NellowTCS/HonzoReader/Docs/assets/images/PlatformIO_new_project.png

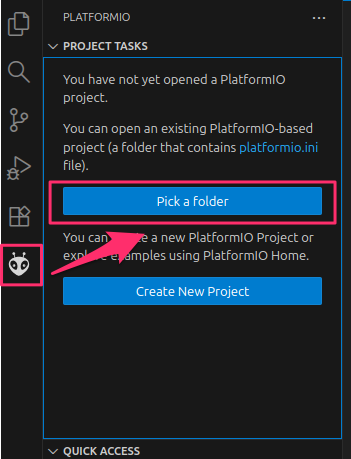
Docs/assets/images/PlatformIO_new_project.png
