NellowTCS/HonzoReader/Resources/Assets/App Loader/Image200.bmp

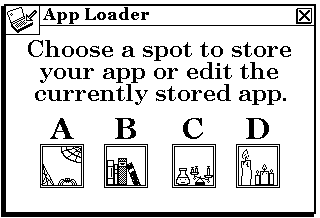
Resources/Assets/App Loader/Image200.bmp
