NellowTCS/HonzoReader/Resources/Assets/Calendar/calendar01.bmp

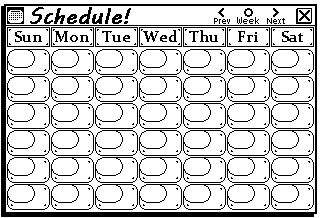
Resources/Assets/Calendar/calendar01.bmp
