NellowTCS/HonzoReader/Resources/Assets/Calendar/calendar02.bmp

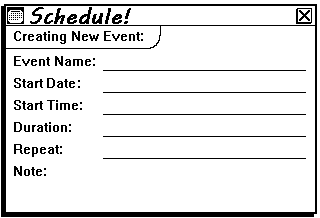
Resources/Assets/Calendar/calendar02.bmp
