NellowTCS/HonzoReader/Resources/Assets/Calendar/calendar03.bmp

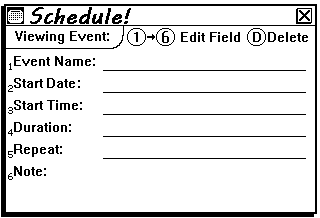
Resources/Assets/Calendar/calendar03.bmp
