NellowTCS/HonzoReader/Resources/Assets/Calendar/calendar04.bmp

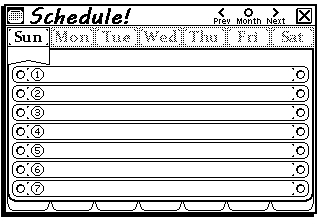
Resources/Assets/Calendar/calendar04.bmp
