NellowTCS/HonzoReader/Resources/Assets/File Wizard/fileWiz0.bmp

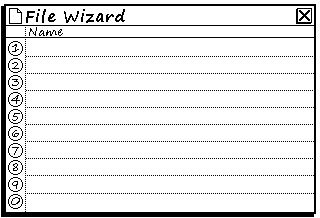
Resources/Assets/File Wizard/fileWiz0.bmp
