NellowTCS/HonzoReader/Resources/Assets/File Wizard/fileWiz1.bmp

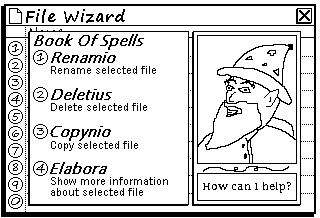
Resources/Assets/File Wizard/fileWiz1.bmp
