NellowTCS/HonzoReader/Resources/Assets/File Wizard/fileWiz3.bmp

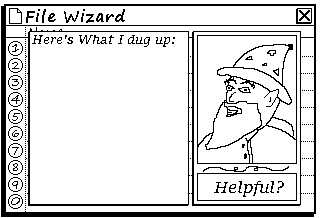
Resources/Assets/File Wizard/fileWiz3.bmp
