NellowTCS/HonzoReader/Resources/Assets/File Wizard/fileWizLite0.bmp

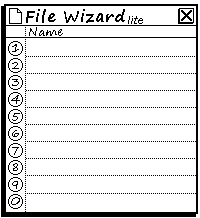
Resources/Assets/File Wizard/fileWizLite0.bmp
