NellowTCS/HonzoReader/Resources/Assets/File Wizard/fileWizLite1.bmp

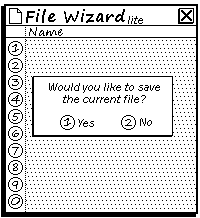
Resources/Assets/File Wizard/fileWizLite1.bmp
