NellowTCS/HonzoReader/Resources/Assets/File Wizard/fileWizLite2.bmp

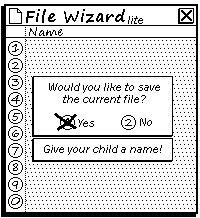
Resources/Assets/File Wizard/fileWizLite2.bmp
