NellowTCS/HonzoReader/Resources/Assets/Font Czar/font0.bmp

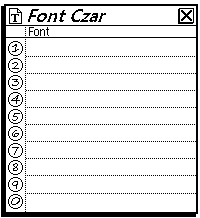
Resources/Assets/Font Czar/font0.bmp
