NellowTCS/HonzoReader/Resources/Assets/Now and Later/nowAndLater0.bmp

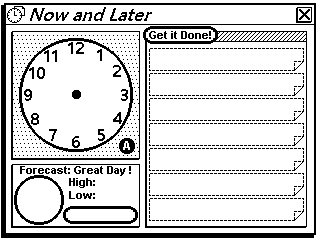
Resources/Assets/Now and Later/nowAndLater0.bmp
