NellowTCS/HonzoReader/Resources/Assets/ScreenSaver/New folder/betterworld_JosieBB.bmp

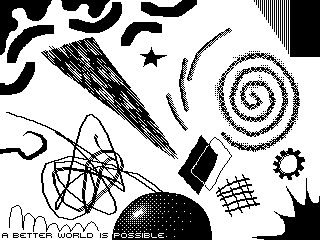
Resources/Assets/ScreenSaver/New folder/betterworld_JosieBB.bmp
