NellowTCS/HonzoReader/Resources/Assets/ScreenSaver/New folder/castle_Nora.bmp

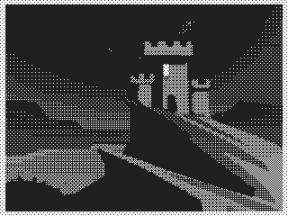
Resources/Assets/ScreenSaver/New folder/castle_Nora.bmp
