NellowTCS/HonzoReader/Resources/Assets/ScreenSaver/New folder/classic (1).bmp

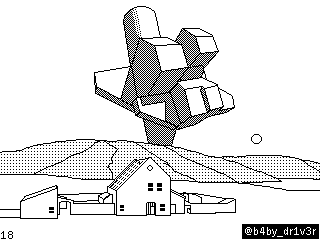
Resources/Assets/ScreenSaver/New folder/classic (1).bmp
