NellowTCS/HonzoReader/Resources/Assets/ScreenSaver/New folder/classic (2).bmp

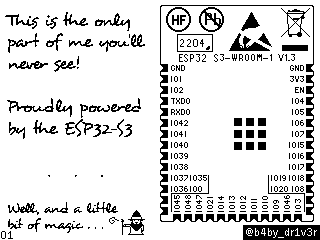
Resources/Assets/ScreenSaver/New folder/classic (2).bmp
