NellowTCS/HonzoReader/Resources/Assets/ScreenSaver/New folder/classic (3).bmp

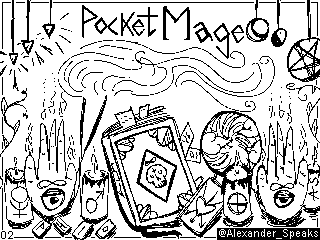
Resources/Assets/ScreenSaver/New folder/classic (3).bmp
