NellowTCS/HonzoReader/Resources/Assets/ScreenSaver/New folder/classic (4).bmp

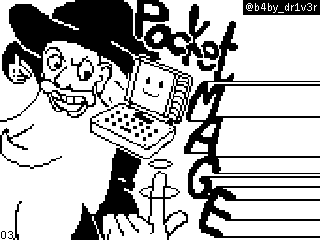
Resources/Assets/ScreenSaver/New folder/classic (4).bmp
