NellowTCS/HonzoReader/Resources/Assets/ScreenSaver/New folder/classic (5).bmp

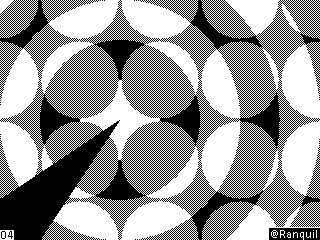
Resources/Assets/ScreenSaver/New folder/classic (5).bmp
