NellowTCS/HonzoReader/Resources/Assets/ScreenSaver/New folder/classic (6).bmp

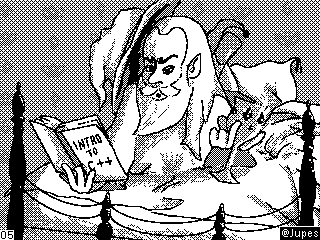
Resources/Assets/ScreenSaver/New folder/classic (6).bmp
