NellowTCS/HonzoReader/Resources/Assets/ScreenSaver/New folder/classic (7).bmp

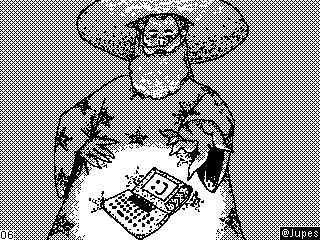
Resources/Assets/ScreenSaver/New folder/classic (7).bmp
