NellowTCS/HonzoReader/Resources/Assets/ScreenSaver/New folder/classic (9).bmp

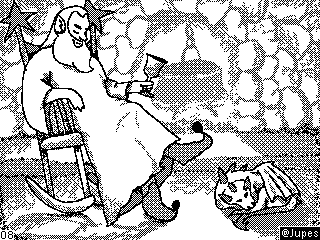
Resources/Assets/ScreenSaver/New folder/classic (9).bmp
