NellowTCS/HonzoReader/Resources/Assets/ScreenSaver/New folder/classic (10).bmp

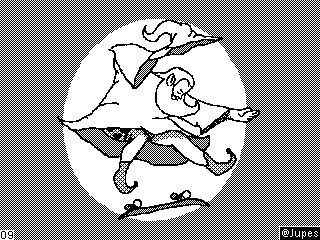
Resources/Assets/ScreenSaver/New folder/classic (10).bmp
