NellowTCS/HonzoReader/Resources/Assets/ScreenSaver/New folder/classic (11).bmp

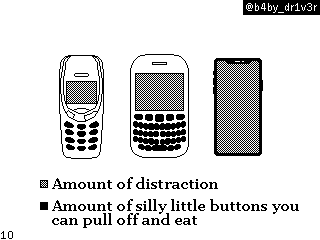
Resources/Assets/ScreenSaver/New folder/classic (11).bmp
