NellowTCS/HonzoReader/Resources/Assets/ScreenSaver/New folder/classic (12).bmp

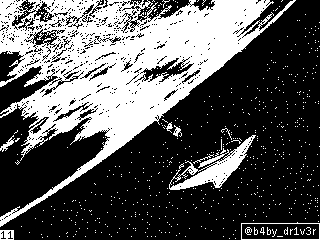
Resources/Assets/ScreenSaver/New folder/classic (12).bmp
