NellowTCS/HonzoReader/Resources/Assets/ScreenSaver/New folder/classic (13).bmp

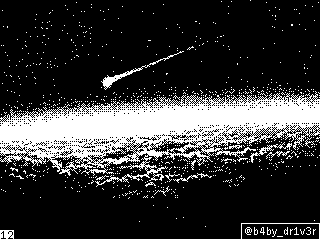
Resources/Assets/ScreenSaver/New folder/classic (13).bmp
