NellowTCS/HonzoReader/Resources/Assets/ScreenSaver/New folder/classic (14).bmp

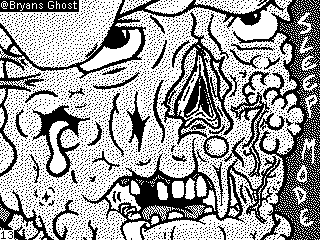
Resources/Assets/ScreenSaver/New folder/classic (14).bmp
