NellowTCS/HonzoReader/Resources/Assets/ScreenSaver/New folder/classic (15).bmp

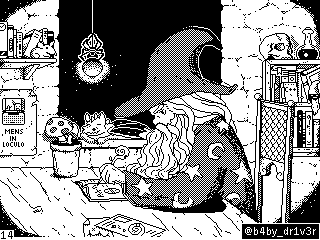
Resources/Assets/ScreenSaver/New folder/classic (15).bmp
