NellowTCS/HonzoReader/Resources/Assets/ScreenSaver/New folder/classic (16).bmp

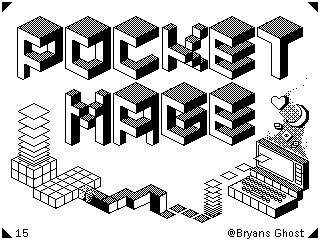
Resources/Assets/ScreenSaver/New folder/classic (16).bmp
