NellowTCS/HonzoReader/Resources/Assets/ScreenSaver/New folder/classic (17).bmp

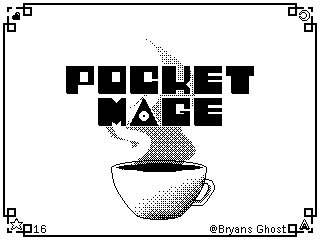
Resources/Assets/ScreenSaver/New folder/classic (17).bmp
