NellowTCS/HonzoReader/Resources/Assets/ScreenSaver/New folder/dragon_TheOddFireFox.bmp

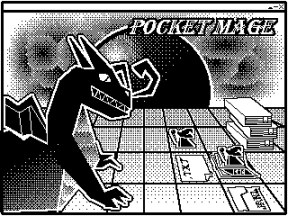
Resources/Assets/ScreenSaver/New folder/dragon_TheOddFireFox.bmp
