NellowTCS/HonzoReader/Resources/Assets/Sleep/sleep0.bmp

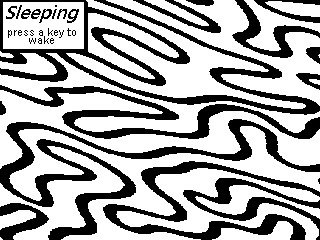
Resources/Assets/Sleep/sleep0.bmp
