NellowTCS/HonzoReader/Resources/Assets/Tasks/1.bmp

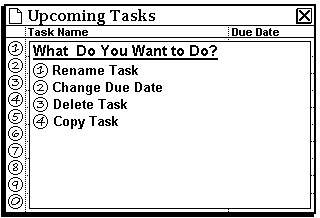
Resources/Assets/Tasks/1.bmp
