NellowTCS/HonzoReader/Resources/Assets/usb/Image20.bmp

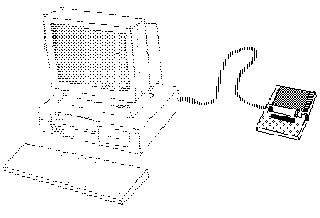
Resources/Assets/usb/Image20.bmp
