NellowTCS/HonzoReader/Docs/assets/images/PlatformIO_installing.png

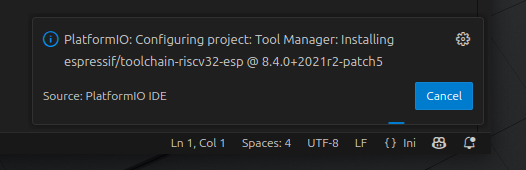
Docs/assets/images/PlatformIO_installing.png
