NellowTCS/HonzoReader/Resources/Assets/Journal/journal0.bmp

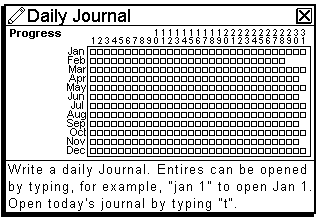
Resources/Assets/Journal/journal0.bmp
