NellowTCS/HonzoReader/Code/PocketMage_V3/src/OS_APPS/JOURNAL.cpp

// AUDIT 1

#include <globals.h>
#if !OTA_APP // POCKETMAGE_OS
enum JournalState {J_MENU, J_TXT};
JournalState CurrentJournalState = J_MENU;

String currentJournal = "";
String bufferEditingFile = PM_SDAUTO().getEditingFile();

void JOURNAL_INIT() {
  CurrentAppState = JOURNAL;
  CurrentJournalState = J_MENU;
  #if POCKETMAGE_HW_VERSION != 2
    EINK().forceSlowFullUpdate(true);
  #endif
  newState = true;
  KB().setKeyboardState(NORMAL);
  bufferEditingFile = PM_SDAUTO().getEditingFile();
}

// File Operations
void loadJournal() {
  PM_SDAUTO().setEditingFile(currentJournal);
  PM_SDAUTO().loadFile();
}

void saveJournal() {
  PM_SDAUTO().setEditingFile(currentJournal);
  PM_SDAUTO().saveFile();
}

String getCurrentJournal() {return currentJournal;}

// Functions
bool isLeapYear(int year) {
  return ((year % 4 == 0) && (year % 100 != 0)) || (year % 400 == 0);
}

void drawJMENU() {
  SDActive = true;
  pocketmage::setCpuSpeed(240);
  delay(50);

  // Display background
  display.setTextColor(GxEPD_BLACK);
  EINK().drawStatusBar("Choose (D)ate or (T)oday");
  display.drawBitmap(0, 0, _journal, 320, 218, GxEPD_BLACK);

  // Update current progress graph
  DateTime now = CLOCK().nowDT();
  String year = String(now.year());

  // 1-indexed matrix to store which days have journal entries
  bool hasJournal[13][32] = {false}; 

  // Read the directory exactly ONCE to prevent SD Card / VFS thrashing
  File dir = global_fs->open("/journal");
  if (dir && dir.isDirectory()) {
    File entry;
    while ((entry = dir.openNextFile())) {
      if (!entry.isDirectory()) {
        String name = entry.name();
        
        // Handle potential leading slash from filesystem driver
        if (name.startsWith("/")) name = name.substring(1);
        
        // Ensure format is exactly YYYYMMDD.txt (12 chars)
        if (name.length() == 12 && name.endsWith(".txt")) {
          if (name.substring(0, 4) == year) {
            int m = name.substring(4, 6).toInt();
            int d = name.substring(6, 8).toInt();
            // Bound checking before writing to array
            if (m >= 1 && m <= 12 && d >= 1 && d <= 31) {
              hasJournal[m][d] = true;
            }
          }
        }
      }
      entry.close();
    }
    dir.close();
  }

  // Pre-calculated Y offsets for each month row
  int yOffsets[12] = {50, 59, 68, 77, 86, 95, 104, 113, 122, 131, 140, 149};
  int daysInMonths[12] = {
    31, isLeapYear(now.year()) ? 29 : 28, 31, 30, 31, 30, 
    31, 31, 30, 31, 30, 31
  };

  // Plot the graph from the matrix
  for (int m = 1; m <= 12; m++) {
    for (int d = 1; d <= daysInMonths[m - 1]; d++) {
      if (hasJournal[m][d]) {
        display.fillRect(91 + (7 * (d - 1)), yOffsets[m - 1], 4, 4, GxEPD_BLACK);
      }
    }
  }

  if (SAVE_POWER) pocketmage::setCpuSpeed(POWER_SAVE_FREQ);
  SDActive = false;
}

// Loops
void processKB_JOURNAL() {
  if (CurrentJournalState == J_MENU && !newState) {
    int currentMillis = millis();
    String uiDate = "";
    
    // 1. Drain the hardware buffer continuously at loop speed
    char inchar = KB().updateKeypress();

    // 2. Only process the actual input if the cooldown has expired
    if (currentMillis - KBBounceMillis >= KB_COOLDOWN) {  
      if (inchar != 0) {
        KBBounceMillis = currentMillis;

        if (inchar == 12 || inchar == 28 || inchar == 19 || inchar == 24) { 
          HOME_INIT();
          return;
        }
        else if (inchar == 't' || inchar == 'T' || inchar == 9 || inchar == 14) {
          DateTime now = CLOCK().nowDT();
          char dateBuf[11];
          snprintf(dateBuf, sizeof(dateBuf), "%02d/%02d/%04d", now.day(), now.month(), now.year());
          uiDate = String(dateBuf);
        }
        else if (inchar == 'd' || inchar == 'D') {
          uiDate = datePrompt("");
          if (CurrentAppState != JOURNAL) return;
        }

        if (uiDate.length() == 10) {
          SDActive = true;
          pocketmage::setCpuSpeed(240);
          delay(50);

          // Convert DD/MM/YYYY from datePrompt into YYYYMMDD for the file system
          String d = uiDate.substring(0, 2);
          String m = uiDate.substring(3, 5);
          String y = uiDate.substring(6, 10);
          String fileName = "/journal/" + y + m + d + ".txt";

          // If file doesn't exist, create it
          if (!global_fs->exists(fileName)) {
            File f = global_fs->open(fileName, FILE_WRITE);
            if (f) f.close();
          }

          currentJournal = fileName;

          if (SAVE_POWER) pocketmage::setCpuSpeed(POWER_SAVE_FREQ);
          SDActive = false;
          
          // Pass execution to the text editor
          TXT_INIT_JournalMode();
          return;
        }
      }
    }

    // 3. Update OLED at true OLED_MAX_FPS, completely independent of keyboard bounce
    currentMillis = millis();
    if (currentMillis - OLEDFPSMillis >= (1000/OLED_MAX_FPS)) {
      OLEDFPSMillis = currentMillis;
      OLED().oledLine("", 0, false);
    }
  }
}

void einkHandler_JOURNAL() {
  switch (CurrentJournalState) {
    case J_MENU:
      if (newState) {
        newState = false;

        EINK().resetDisplay(); // Clear the uninitialized buffer correctly
        drawJMENU();

        EINK().multiPassRefresh(2);
      }
      break;
    default:
      CurrentJournalState = J_MENU;
      break;
  } 
}
#endif
