NellowTCS/HonzoReader/Resources/Subsystem Tests/BuzzerTest_SuperMario/BuzzerTest_SuperMario.ino

#include <Buzzer.h>

Buzzer buzzer(17);

void setup() {}

void loop() {
  buzzer.begin(100);

  buzzer.sound(NOTE_E7, 80);
  buzzer.sound(NOTE_E7, 80);
  buzzer.sound(0, 80);
  buzzer.sound(NOTE_E7, 80);
  buzzer.sound(0, 80);
  buzzer.sound(NOTE_C7, 80);
  buzzer.sound(NOTE_E7, 80);
  buzzer.sound(0, 80);
  buzzer.sound(NOTE_G7, 80);
  buzzer.sound(0, 240);
  buzzer.sound(NOTE_G6, 80);
  buzzer.sound(0, 240);
  buzzer.sound(NOTE_C7, 80);
  buzzer.sound(0, 160);
  buzzer.sound(NOTE_G6, 80);
  buzzer.sound(0, 160);
  buzzer.sound(NOTE_E6, 80);
  buzzer.sound(0, 160);
  buzzer.sound(NOTE_A6, 80);
  buzzer.sound(0, 80);
  buzzer.sound(NOTE_B6, 80);
  buzzer.sound(0, 80);
  buzzer.sound(NOTE_AS6, 80);
  buzzer.sound(NOTE_A6, 80);
  buzzer.sound(0, 80);
  buzzer.sound(NOTE_G6, 100);
  buzzer.sound(NOTE_E7, 100);
  buzzer.sound(NOTE_G7, 100);
  buzzer.sound(NOTE_A7, 80);
  buzzer.sound(0, 80);
  buzzer.sound(NOTE_F7, 80);
  buzzer.sound(NOTE_G7, 80);
  buzzer.sound(0, 80);
  buzzer.sound(NOTE_E7, 80);
  buzzer.sound(0, 80);
  buzzer.sound(NOTE_C7, 80);
  buzzer.sound(NOTE_D7, 80);
  buzzer.sound(NOTE_B6, 80);
  buzzer.sound(0, 160);
  buzzer.sound(NOTE_C7, 80);
  buzzer.sound(0, 160);
  buzzer.sound(NOTE_G6, 80);
  buzzer.sound(0, 160);
  buzzer.sound(NOTE_E6, 80);
  buzzer.sound(0, 160);
  buzzer.sound(NOTE_A6, 80);
  buzzer.sound(0, 80);
  buzzer.sound(NOTE_B6, 80);
  buzzer.sound(0, 80);
  buzzer.sound(NOTE_AS6, 80);
  buzzer.sound(NOTE_A6, 80);
  buzzer.sound(0, 80);
  buzzer.sound(NOTE_G6, 100);
  buzzer.sound(NOTE_E7, 100);
  buzzer.sound(NOTE_G7, 100);
  buzzer.sound(NOTE_A7, 80);
  buzzer.sound(0, 80);
  buzzer.sound(NOTE_F7, 80);
  buzzer.sound(NOTE_G7, 80);
  buzzer.sound(0, 80);
  buzzer.sound(NOTE_E7, 80);
  buzzer.sound(0, 80);
  buzzer.sound(NOTE_C7, 80);
  buzzer.sound(NOTE_D7, 80);
  buzzer.sound(NOTE_B6, 80);
  buzzer.sound(0, 160);

  buzzer.end(2000);
}
