NellowTCS/HonzoReader/Resources/Subsystem Tests/MPR121test/MPR121test.ino

#include <Wire.h>
#include "Adafruit_MPR121.h"

#ifndef _BV
#define _BV(bit) (1 << (bit)) 
#endif

#define I2C_SCL       35
#define I2C_SDA       36
#define MPR121_ADDR   0x5A

// You can have up to 4 on one i2c bus but one is enough for testing!
Adafruit_MPR121 cap = Adafruit_MPR121();

// Keeps track of the last pins touched
// so we know when buttons are 'released'
uint16_t lasttouched = 0;
uint16_t currtouched = 0;

void setup() {
  Serial.begin(9600);
  Wire.begin(I2C_SDA, I2C_SCL);

  while (!Serial) { // needed to keep leonardo/micro from starting too fast!
    delay(10);
  }
  
  Serial.println("Adafruit MPR121 Capacitive Touch sensor test"); 
  
  // Default address is 0x5A, if tied to 3.3V its 0x5B
  // If tied to SDA its 0x5C and if SCL then 0x5D
  if (!cap.begin(MPR121_ADDR)) {
    Serial.println("MPR121 not found, check wiring?");
    while (1);
  }
  Serial.println("MPR121 found!");

  cap.setAutoconfig(true);
  delay(1000);
  //Serial.println("MPR121 being initialized");
  //cap.setThreshholds(1,1);
}

void loop() {
  // Get the currently touched pads
  currtouched = cap.touched();
  
  for (uint8_t i=0; i<12; i++) {
    // it if *is* touched and *wasnt* touched before, alert!
    if ((currtouched & _BV(i)) && !(lasttouched & _BV(i)) ) {
      Serial.print(i); Serial.println(" touched");
    }
    // if it *was* touched and now *isnt*, alert!
    if (!(currtouched & _BV(i)) && (lasttouched & _BV(i)) ) {
      Serial.print(i); Serial.println(" released");
    }
  }

  // reset our state
  lasttouched = currtouched;

  // comment out this line for detailed data from the sensor!
  return;
  
  // debugging info, what
  Serial.print("\t\t\t\t\t\t\t\t\t\t\t\t\t 0x"); Serial.println(cap.touched(), HEX);
  Serial.print("Filt: ");
  for (uint8_t i=0; i<12; i++) {
    Serial.print(cap.filteredData(i)); Serial.print("\t");
  }
  Serial.println();
  Serial.print("Base: ");
  for (uint8_t i=0; i<12; i++) {
    Serial.print(cap.baselineData(i)); Serial.print("\t");
  }
  Serial.println();
  
  // put a delay so it isn't overwhelming
  delay(100);
}
