NellowTCS/HonzoReader/Resources/Subsystem Tests/GDEQ031T10-Arduino/Ap_29demo.h

#include <pgmspace.h>
//32*32(y=32-1,x=32-1)
const unsigned char gImage_num0[128]PROGMEM = { /* 0X00,0X01,0X20,0X00,0X20,0X00, */
0XFF,0XFF,0XFF,0XFF,0XFF,0XFF,0XFF,0XFF,0XFF,0XFF,0XFF,0XFF,0XFF,0XFF,0XFF,0XFF,
0XFF,0XFF,0XFF,0XFF,0XFF,0XFF,0XFF,0XFF,0XFF,0XFF,0XFF,0XFF,0XFF,0XFF,0XFF,0XFF,
0XFF,0XFC,0X0F,0XFF,0XFF,0XF8,0XC7,0XFF,0XFF,0XF1,0XE3,0XFF,0XFF,0XE3,0XF1,0XFF,
0XFF,0XE3,0XF1,0XFF,0XFF,0XE3,0XF9,0XFF,0XFF,0XC7,0XF8,0XFF,0XFF,0XC7,0XF8,0XFF,
0XFF,0XC7,0XF8,0XFF,0XFF,0XC7,0XF8,0XFF,0XFF,0XC7,0XF8,0XFF,0XFF,0XC7,0XF8,0XFF,
0XFF,0XC7,0XF8,0XFF,0XFF,0XC7,0XF8,0XFF,0XFF,0XC7,0XF8,0XFF,0XFF,0XE3,0XF9,0XFF,
0XFF,0XE3,0XF1,0XFF,0XFF,0XE3,0XF1,0XFF,0XFF,0XF1,0XE3,0XFF,0XFF,0XF8,0XC7,0XFF,
0XFF,0XFC,0X0F,0XFF,0XFF,0XFF,0XFF,0XFF,0XFF,0XFF,0XFF,0XFF,0XFF,0XFF,0XFF,0XFF,
};
const unsigned char gImage_num1[128]PROGMEM = { /* 0X00,0X01,0X20,0X00,0X20,0X00, */
0XFF,0XFF,0XFF,0XFF,0XFF,0XFF,0XFF,0XFF,0XFF,0XFF,0XFF,0XFF,0XFF,0XFF,0XFF,0XFF,
0XFF,0XFF,0XFF,0XFF,0XFF,0XFF,0XFF,0XFF,0XFF,0XFF,0XFF,0XFF,0XFF,0XFF,0XFF,0XFF,
0XFF,0XFF,0X3F,0XFF,0XFF,0XFE,0X3F,0XFF,0XFF,0XE0,0X3F,0XFF,0XFF,0XFE,0X3F,0XFF,
0XFF,0XFE,0X3F,0XFF,0XFF,0XFE,0X3F,0XFF,0XFF,0XFE,0X3F,0XFF,0XFF,0XFE,0X3F,0XFF,
0XFF,0XFE,0X3F,0XFF,0XFF,0XFE,0X3F,0XFF,0XFF,0XFE,0X3F,0XFF,0XFF,0XFE,0X3F,0XFF,
0XFF,0XFE,0X3F,0XFF,0XFF,0XFE,0X3F,0XFF,0XFF,0XFE,0X3F,0XFF,0XFF,0XFE,0X3F,0XFF,
0XFF,0XFE,0X3F,0XFF,0XFF,0XFE,0X3F,0XFF,0XFF,0XFE,0X3F,0XFF,0XFF,0XFC,0X1F,0XFF,
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
0XFF,0XFF,0XFF,0XFF,0XFF,0XFF,0XFF,0XFF,0XFF,0XFF,0XFF,0XFF,0XFF,0XFF,0XFF,
0XFF,0XFF,0XFF,0XFF,0XFF,0XFF,0XFF,0XFF,0XFF,0XFF,0XFF,0XFF,0XFF,0XFF,0XFF,0XFF,
0XFF,0XFF,0XFF,0XFF,0XFF,0XFF,0XFF,0XFF,0XFF,0XFF,0XFF,0XFF,0XFF,0XFF,0XFF,
0XFF,0XFF,0XFF,0XFF,0XFF,0XFF,0XFF,0XFF,0XFF,0XFF,0XFF,0XFF,0XFF,0XFF,0XFF,0XFF,
0XFF,0XFF,0XFF,0XFF,0XFF,0XFF,0XFF,0XFF,0XFF,0XFF,0XFF,0XFF,0XFF,0XFF,0XFF,
0XFF,0XFF,0XFF,0XFF,0XFF,0XFF,0XFF,0XFF,0XFF,0XFF,0XFF,0XFF,0XFF,0XFF,0XFF,0XFF,
0XFF,0XFF,0XFF,0XFF,0XFF,0XFF,0XFF,0XFF,0XFF,0XFF,0XFF,0XFF,0XFF,0XFF,0XFF,
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
